earp123/Project-Blue-Frog/src/tdma_console/soak_log.h

/*
 * soak_log - binary soak-run logger for the field console.
 *
 * Records what the radio actually did, per packet, fast enough to keep up at
 * the 20 ms production slot. Three decisions drive the design:
 *
 * 1. Fixed 64-byte binary records, not CSV. The payload alone is 40 bytes,
 *    which as hex text would be 80 characters before any telemetry; formatting
 *    it per packet costs far more CPU than a memcpy. 64 B also divides 512
 *    exactly, so eight records fill a FAT sector with no waste and no
 *    partial-sector rewrite. Text formatting happens offline in the decoder
 *    (tools/decode_soak_log.py), where it is free.
 *
 * 2. The producer never touches the card. Records go into a k_msgq ring; a
 *    dedicated low-priority writer thread drains it into sd_log. A card stall
 *    therefore stalls only the writer, never the UI loop, and never the radio
 *    thread (which is cooperative and outranks both regardless).
 *
 * 3. Logging failure is non-fatal. A missing or full card must not abort a
 *    radio test: the ring simply drops, the drop count is surfaced on screen,
 *    and the soak keeps running.
 *
 * Rate budget at the 20 ms slot (80 ms frame, 4 units): 3 RX + 1 TX per frame
 * = 50 records/s = 3.2 KB/s = ~6 sector writes/s. Comfortably inside what the
 * card demonstrated, with the ring absorbing the sync stalls.
 *
 * SPDX-License-Identifier: Apache-2.0
 */

#ifndef SOAK_LOG_H_
#define SOAK_LOG_H_

#include <zephyr/kernel.h>
#include <zephyr/toolchain.h>
#include <stdbool.h>
#include <stdint.h>

#include "tdma.h"
#include "sd_log.h"

/*
 * On-disk format version; bump on any record-layout change.
 *
 * v2: STATS records gained a typed payload overlay (struct soak_stats).
 *     v1 packed ten uint32 counters into the payload and squeezed the phase
 *     error and clock-rate estimate into the record's rssi/snr header fields —
 *     but ppm is an int32 and snr is an int8, so it railed at ±127 and the
 *     measurement was destroyed. phase_err had the same latent problem
 *     (int16 cannot hold the ±frame/2 range). Both are now int32. Room was
 *     made by dropping rx_ok/missed/dup, which the decoder derives from the
 *     RX records' frame-counter continuity anyway.
 */
#define SOAK_LOG_VERSION	2
#define SOAK_LOG_MAGIC		0x4B414F53UL	/* "SOAK", little-endian */

/* Eight records per 512-byte sector. Keep this exact. */
#define SOAK_REC_SIZE		64

/*
 * Ring depth in records. 128 * 64 B = 8 KB, about 2.5 s of headroom at the
 * 20 ms-slot worst case — sized to swallow a card sync stall whole, since
 * anything the ring drops is data the run can never recover.
 */
#define SOAK_LOG_RING_DEPTH	128

enum soak_rec_type {
	SOAK_REC_META = 1,	/* run parameters; always record 0 */
	SOAK_REC_RX = 2,	/* one received packet */
	SOAK_REC_TX = 3,	/* one submitted transmit */
	SOAK_REC_STATS = 4,	/* periodic engine counter snapshot */
};

/* flags bits */
#define SOAK_F_NO_CTR	BIT(0)	/* frame_ctr not meaningful (TX records) */

/*
 * The one on-disk record. Every field is naturally aligned at its offset, so
 * __packed changes nothing about layout here — it only pins the size against
 * accidental padding on a compiler change.
 */
struct soak_rec {
	uint8_t  type;		/* enum soak_rec_type */
	uint8_t  slot_id;
	uint8_t  sync_state;	/* enum tdma_sync_state */
	uint8_t  flags;
	uint32_t t_us;		/* slot-clock time: RX = DIO1 edge, TX = submit */
	uint16_t frame_ctr;
	int16_t  rssi;		/* dBm */
	int8_t   snr;		/* dB */
	uint8_t  rsvd[3];
	uint32_t seq;		/* monotonic; a gap means the ring dropped */
	uint32_t uptime_ms;	/* wall-clock correlation between the two units */
	uint8_t  payload[TDMA_PAYLOAD_LEN];	/* 40 B: RX/TX data, or packed
						 * counters for META/STATS */
} __packed;

BUILD_ASSERT(sizeof(struct soak_rec) == SOAK_REC_SIZE,
	     "soak_rec must stay 64 B so 8 pack into a 512 B sector");
BUILD_ASSERT(SD_LOG_BLOCK % SOAK_REC_SIZE == 0,
	     "record size must divide the FAT sector exactly");

/*
 * STATS payload overlay (little-endian, written into soak_rec.payload).
 * Exactly 40 bytes: seven raw engine counters plus the three sync-quality
 * measurements, all int32/uint32 so nothing is clamped.
 *
 * The counters are logged ABSOLUTE, not per-soak: tdma_start() deliberately
 * does not reset the engine's telemetry, so a second soak in the same boot
 * continues counting. Per-run figures come from differencing the first and
 * last STATS record, and the runner emits a baseline record at t=0 so that
 * difference is exact.
 */
struct soak_stats {
	uint32_t tx_done;
	uint32_t rx_done;
	uint32_t rx_crc_err;
	uint32_t rx_bad_header;
	uint32_t slot_timeouts;
	uint32_t stale_retx;
	uint32_t busy_timeouts;
	int32_t  phase_err_us;	/* secondary: last beacon phase error */
	int32_t  ppm;		/* secondary: local-vs-master clock rate */
	uint32_t evt_dt_us;	/* last boundary-to-DIO1 delay */
} __packed;

BUILD_ASSERT(sizeof(struct soak_stats) <= TDMA_PAYLOAD_LEN,
	     "soak_stats must fit the record payload");

/* META payload overlay (little-endian, written into soak_rec.payload). */
struct soak_meta {
	uint32_t magic;
	uint16_t version;
	uint8_t  role;		/* enum tdma_role */
	uint8_t  slot_id;
	uint32_t freq_hz;
	uint32_t slot_us;
	uint32_t frame_us;
	uint32_t toa_us;
	uint8_t  sf;
	uint8_t  cr;		/* 4/(4+cr) */
	uint16_t bw_khz;
	int8_t   tx_power_dbm;
	uint8_t  slot_count;
	uint8_t  payload_len;
	uint8_t  preamble_syms;
	uint32_t uptime_ms;
} __packed;

struct soak_log_status {
	bool active;
	uint32_t queued;	/* records handed to the ring */
	uint32_t written;	/* records the writer pushed to sd_log */
	uint32_t dropped;	/* ring-full drops (producer side) */
	uint32_t bytes;
	int err;		/* last writer error, 0 if healthy */
	const char *err_stage;	/* "disk" / "mount" / "open" / "write" / "close"
				 * when err is set */
	const char *path;
};

/*
 * Open a session file and queue the META record. Returns 0, or a negative
 * errno if the card is unusable — the caller should carry on with the soak
 * regardless and simply show the failure.
 *
 * The file name encodes the run: "<PWR>_<DUR>_NNN.BIN" with M/P for the
 * power sign (M9 = -9 dBm, P22 = +22 dBm) and the duration in minutes/hours
 * ("5M", "30M", "2H"; "CT" = continuous, duration_ms == 0). dir is a bare
 * top-level directory name ("DRAWER0"...) or ""/NULL for the card root; a
 * missing drawer is created when the file opens.
 */
int soak_log_start(enum tdma_role role, uint8_t slot_id, int8_t tx_power_dbm,
		   uint32_t duration_ms, const char *dir);

/* ---- Card file operations (browser back end) --------------------------- *
 * All card I/O runs on the writer thread — the FatFs LFN working buffer is
 * a single static (not thread-safe), and a sick card must never stall the
 * UI. So the browser submits an op and polls for completion from its 20 ms
 * loop; one op may be in flight at a time.
 */
#define SD_FSOP_NAME_MAX 32	/* entry name (truncating longer LFNs) */

enum sd_fsop_op {
	SD_FSOP_LIST,		/* a = directory path; fills ents */
	SD_FSOP_UNLINK,		/* a = path */
	SD_FSOP_MKDIR,		/* a = path */
	SD_FSOP_RENAME,		/* a -> b (also moves across directories; a
				 * missing destination drawer is created) */
	SD_FSOP_SUMMARY,	/* a = directory path; see sd_fsop_submit_summary */
};

struct sd_dirent {
	char name[SD_FSOP_NAME_MAX];
	uint32_t size;
	bool is_dir;
};

/*
 * Queue one op. a/b are full VFS paths ("/SD:/..."). For LIST, ents/cap
 * receive the entries (directories first, then names sorted); the buffer is
 * owned by the caller and must not be read until the op completes. Returns
 * -EBUSY if an op is already in flight.
 */
int sd_fsop_submit(enum sd_fsop_op op, const char *a, const char *b,
		   struct sd_dirent *ents, int cap);

/* One directory's log summary plus volume space (SD_FSOP_SUMMARY). */
struct sd_summary {
	uint32_t bin_count;		/* *.BIN files in the directory */
	char newest[SD_FSOP_NAME_MAX];	/* last *.BIN in directory order; ""
					 * if none */
	uint32_t free_mib;		/* fs_statvfs; valid if vfs_err == 0 */
	uint32_t total_mib;
	int vfs_err;
};

/*
 * Queue a summary of dir: count its *.BIN files, note the last one in
 * directory order, and fs_statvfs the volume.
 *
 * This is not a LIST because LIST stops at the caller's buffer and sorts by
 * name. FAT appends new entries at the end of the directory, so on a card
 * with many logs a capped listing drops exactly the newest ones. This op walks
 * the whole directory and needs no entry buffer. "Last in directory order" is
 * the newest file unless something deleted entries earlier in the directory
 * and a later file reused the gap. The field unit never deletes; the console's
 * file browser can.
 *
 * Same one-deep slot and rules as sd_fsop_submit(): out is written on the
 * writer thread and must not be read until sd_fsop_poll() reports completion
 * (count = bin_count, saturated at INT_MAX).
 */
int sd_fsop_submit_summary(const char *dir, struct sd_summary *out);

/* True once the op has finished; result (0 / -errno) and, for LIST, the
 * entry count are returned and the slot frees for the next op.
 */
bool sd_fsop_poll(int *result, int *count);

/* Producers. All are non-blocking and safe to call whether or not a log is
 * open; they drop (and count) rather than wait.
 */
void soak_log_rx(const struct tdma_rx_msg *msg, uint8_t sync_state);

/*
 * Record one *transmitted* packet. Call this when the engine's tx_done has
 * actually advanced, not when a payload is staged: tdma_tx_submit() succeeds
 * whenever the stage buffer is free, which is far more often than the engine
 * transmits, and every extra staged payload is overwritten before its slot.
 * Logging at stage time produced ~2.4 records per real transmission, two
 * thirds of them for bytes that never reached the air.
 */
void soak_log_tx(const uint8_t payload[TDMA_PAYLOAD_LEN], uint8_t slot_id,
		 uint8_t sync_state);

void soak_log_stats(const struct tdma_telemetry *t);

/* Drain the ring, flush and close. Blocks briefly for the writer to finish. */
int soak_log_stop(void);

void soak_log_get_status(struct soak_log_status *out);

#endif /* SOAK_LOG_H_ */
